Szybet/Yatchy/img/Yatchy-small.png

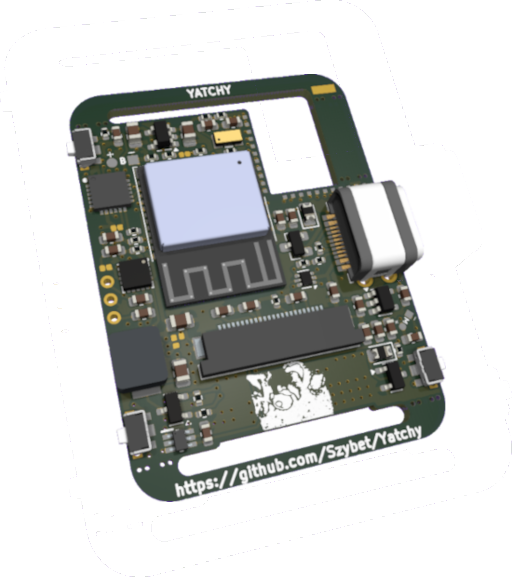
img/Yatchy-small.png
