Szybet/Yatchy/3D/cases/patches/1/better_strap_dot.stl

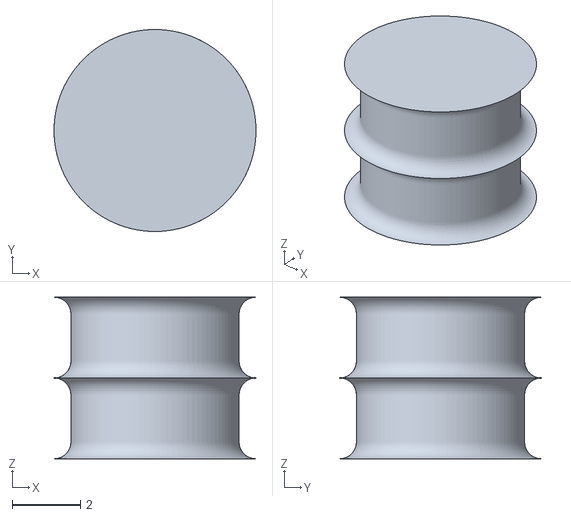
[picture p44: CAD file, 2025-07-04]
3D/cases/patches/1/better_strap_dot.stl
5.94 x 5.94 x 4.75
