Szybet/Yatchy/3D/cases/Szybet-side/3D/motor cover.step

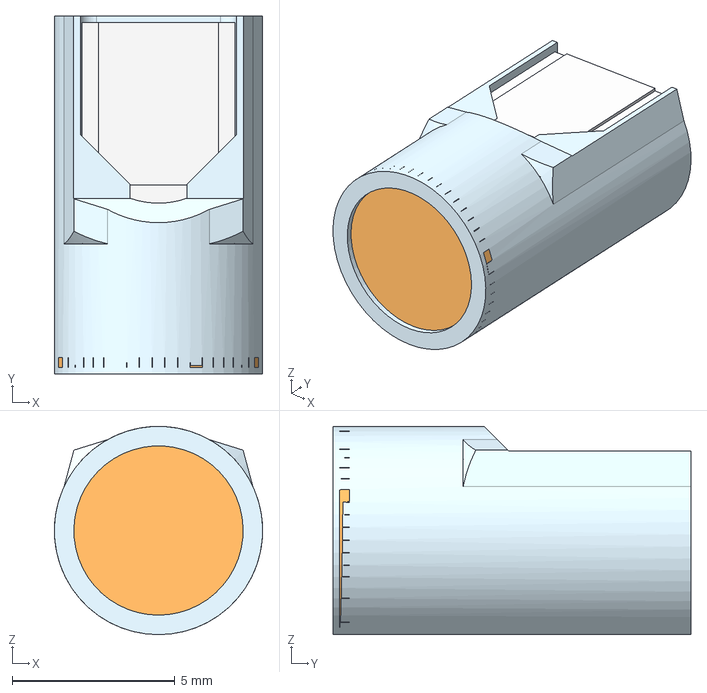
[picture p45: CAD file, 2025-03-13]
3D/cases/Szybet-side/3D/motor cover.step
6.40 x 11.0 x 6.40 mm
