Szybet/Yatchy/hardware/kicad/Yatchy/3d-Models/display_eink.step

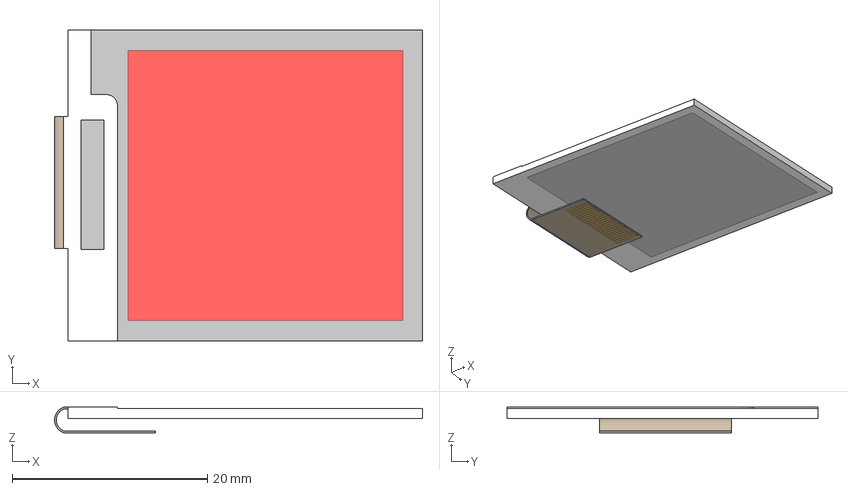
[picture p46: CAD file, 2025-08-27]
hardware/kicad/Yatchy/3d-Models/display_eink.step
37.7 x 31.8 x 2.63 mm
