Szybet/Yatchy/3D/cases/Szybet-side/3D/strap.step

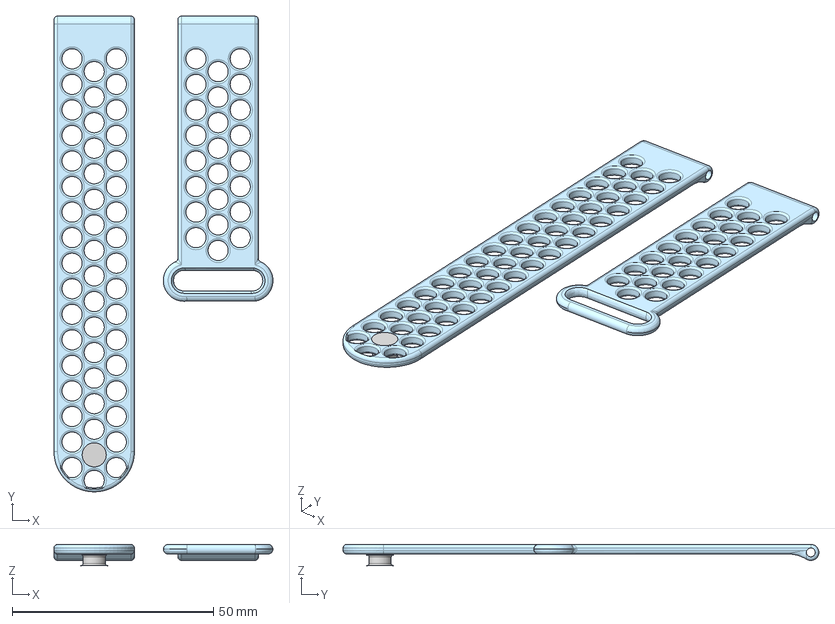
[picture p47: CAD file, 2025-03-13]
3D/cases/Szybet-side/3D/strap.step
54.4 x 118.3 x 5.28 mm
