Szybet/Yatchy/hardware/kicad/Yatchy/3d-Models/EVP-AKE31A.stp

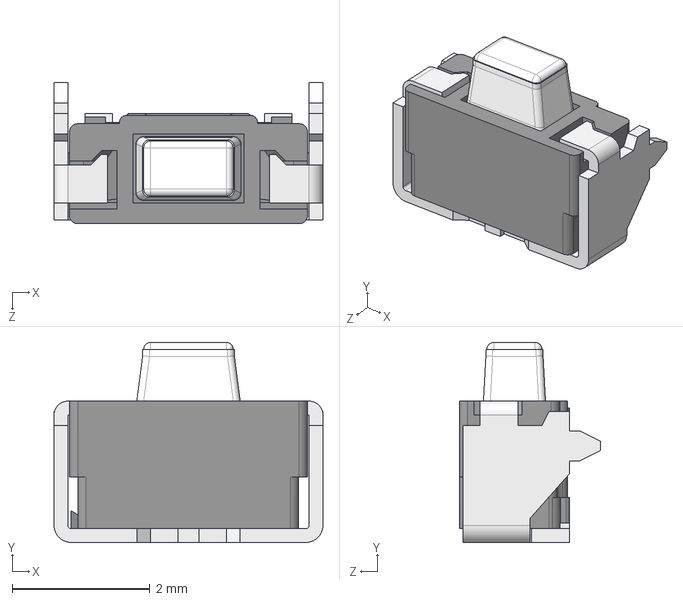
[picture p48: CAD file, 2024-11-07]
hardware/kicad/Yatchy/3d-Models/EVP-AKE31A.stp
3.90 x 2.90 x 2.05 mm
