Szybet/Yatchy/3D/cases/Szybet-side/3D/module led cover.step

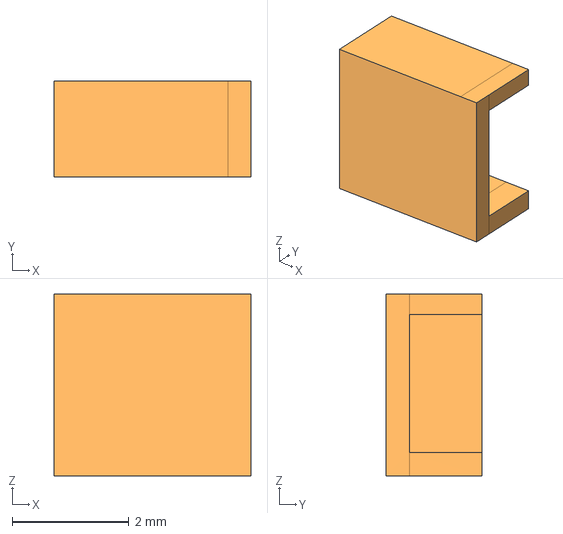
[picture p49: CAD file, 2025-03-13]
3D/cases/Szybet-side/3D/module led cover.step
3.38 x 1.64 x 3.12 mm
