Szybet/Yatchy/hardware/kicad/Yatchy/3d-Models/CLMVC-FKA-CL1D1L71BB7C3C3_CRE.step

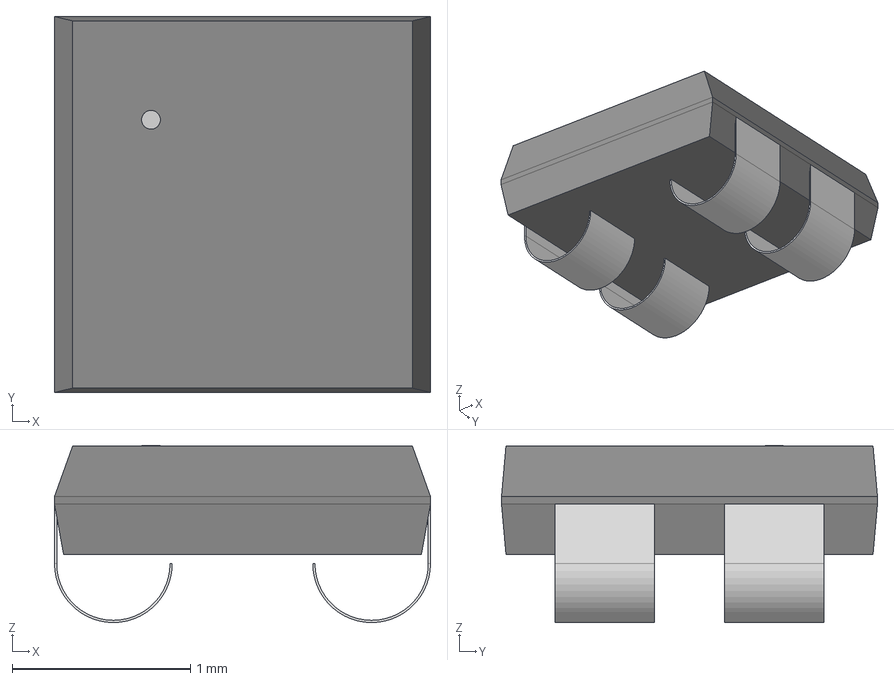
[picture p50: CAD file, 2024-11-07]
hardware/kicad/Yatchy/3d-Models/CLMVC-FKA-CL1D1L71BB7C3C3_CRE.step
2.11 x 2.11 x 0.993 mm
