Szybet/Yatchy/hardware/kicad/Yatchy/3d-Models/USB4730-GF-A-KIT.stp

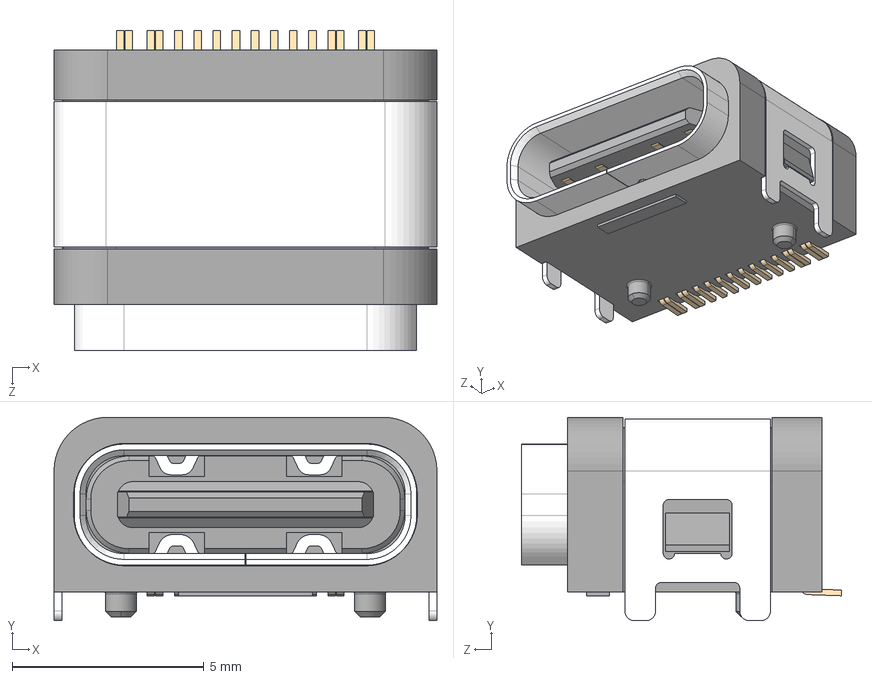
[picture p51: CAD file, 2024-11-07]
hardware/kicad/Yatchy/3d-Models/USB4730-GF-A-KIT.stp
10.00 x 5.31 x 8.36 mm
Part61^USB4730_ASM
