Szybet/Yatchy/hardware/kicad/Yatchy/3d-Models/SFV24R-4STBE1HLF.stp

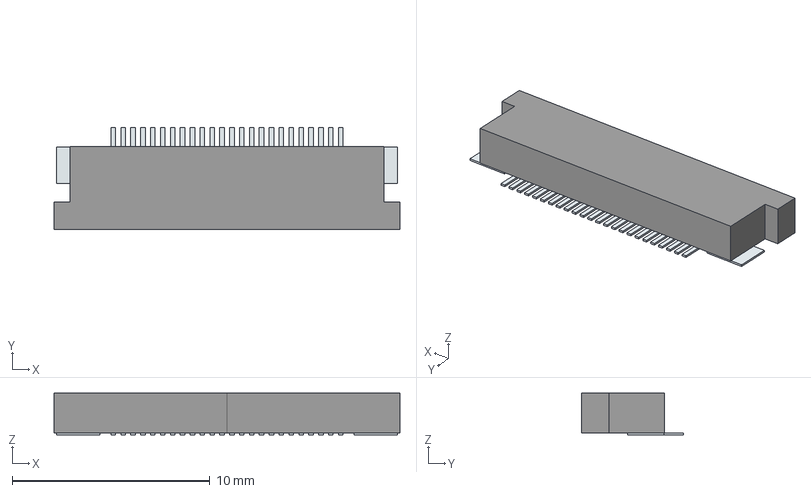
[picture p52: CAD file, 2024-11-07]
hardware/kicad/Yatchy/3d-Models/SFV24R-4STBE1HLF.stp
17.5 x 5.17 x 2.10 mm
Pins
