Szybet/Yatchy/hardware/kicad/Yatchy/3d-Models/ESP32-C6-MINI-1-N4.step

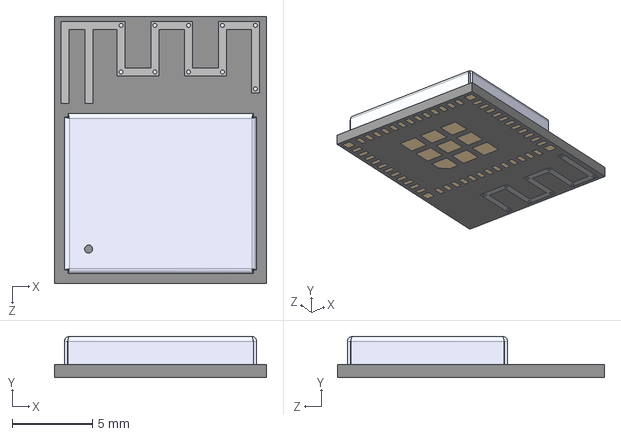
[picture p53: CAD file, 2024-11-07]
hardware/kicad/Yatchy/3d-Models/ESP32-C6-MINI-1-N4.step
13.2 x 2.55 x 16.6 mm
