Szybet/Yatchy/hardware/kicad/Yatchy/3d-Models/inductor.step

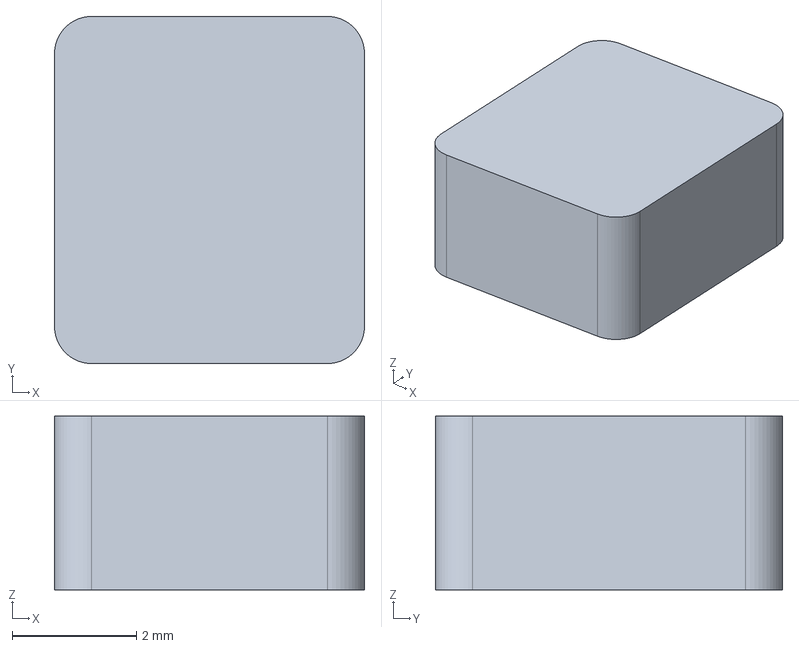
[picture p54: CAD file, 2024-11-07]
hardware/kicad/Yatchy/3d-Models/inductor.step
5.00 x 5.60 x 2.80 mm
