Szybet/Yatchy/hardware/kicad/Yatchy/3d-Models/RV-3028-C7_32.768kHz_1ppm_TA_QC.stp

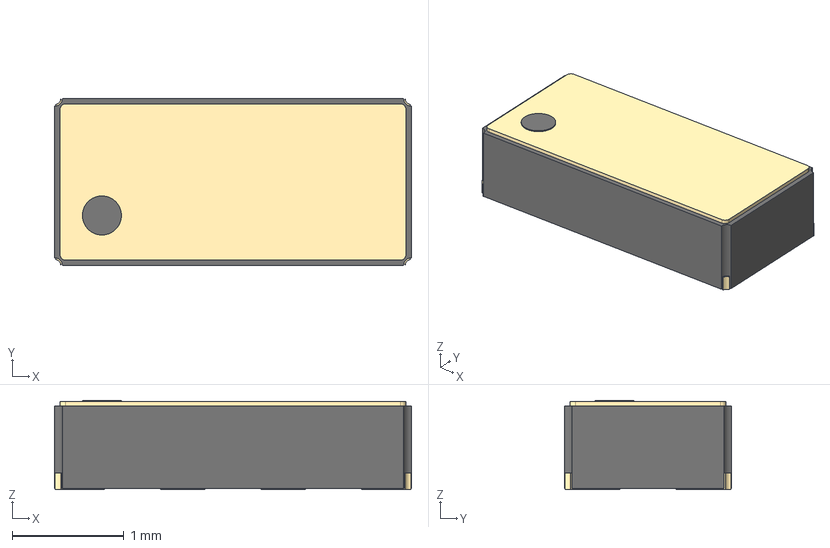
[picture p55: CAD file, 2024-11-07]
hardware/kicad/Yatchy/3d-Models/RV-3028-C7_32.768kHz_1ppm_TA_QC.stp
3.20 x 1.50 x 0.8 mm
Rect2
Rect3
Rect4
Rect5
Terminal
