Szybet/Yatchy/hardware/kicad/Yatchy/3d-Models/BAT54TW-7-F.stp

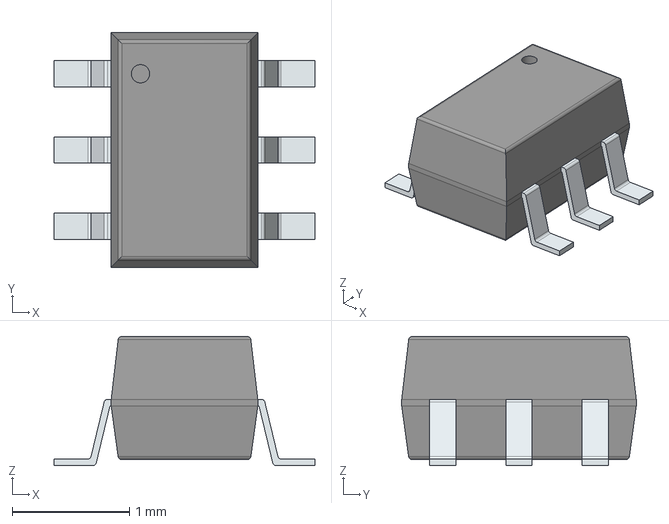
[picture p56: CAD file, 2024-11-07]
hardware/kicad/Yatchy/3d-Models/BAT54TW-7-F.stp
2.23 x 2.00 x 1.10 mm
PinsArrayLR
