Szybet/Yatchy/hardware/kicad/Yatchy/3d-Models/BMA456.stp

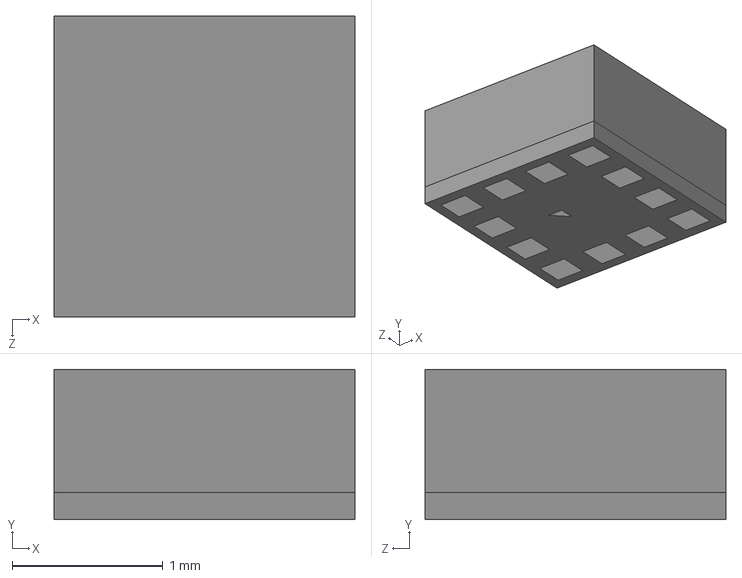
[picture p57: CAD file, 2024-11-07]
hardware/kicad/Yatchy/3d-Models/BMA456.stp
2.00 x 1.00 x 2.00 mm
