Szybet/Yatchy/hardware/kicad/Yatchy/3d-Models/BMA530.stp

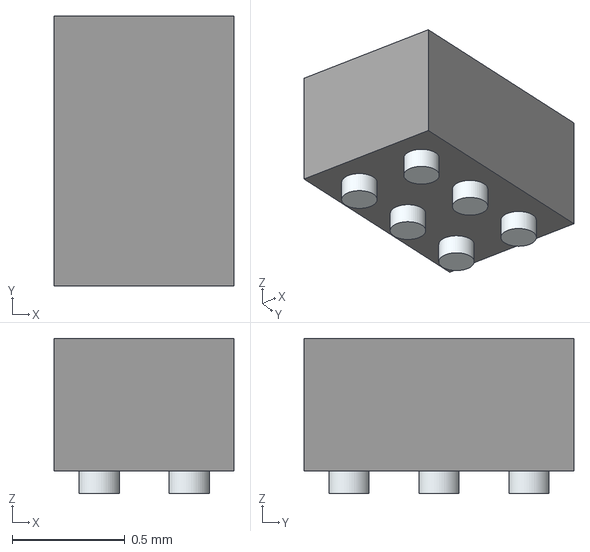
[picture p58: CAD file, 2024-11-07]
hardware/kicad/Yatchy/3d-Models/BMA530.stp
0.8 x 1.20 x 0.69 mm
Pins
